zultron/taz_cramps_machinekit/machinekit_config/3D.postgui.hal

net e0.temp.set  => pyvcp.e0.temp.set
net e0.temp.meas => pyvcp.e0.temp.meas
net e1.temp.set  => pyvcp.e1.temp.set
net e1.temp.meas => pyvcp.e1.temp.meas
net bed.temp.set  => pyvcp.bed.temp.set
net bed.temp.meas => pyvcp.bed.temp.meas
